rookie/johns-car-project/Assets/2014_8_4_gauge_320X240.bmp

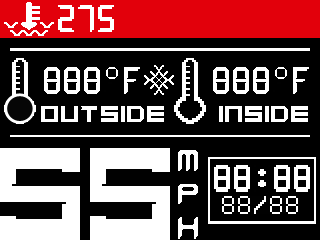
Assets/2014_8_4_gauge_320X240.bmp
