rookie/johns-car-project/Assets/gauge1.bmp

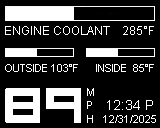
Assets/gauge1.bmp
