rookie/johns-car-project/Processing/JohnsCarProjectUI/gaugev1.bmp

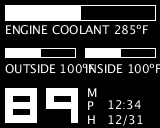
Processing/JohnsCarProjectUI/gaugev1.bmp
