rookie/johns-car-project/johnsCarProject/smallFont.ino

//16x12
const unsigned char PROGMEM icon_degree[] =
{
  B00011111, B10000000,
  B00111111, B11000000,
  B01100000, B01100000,
  B11000000, B00110000,
  B11000000, B00110000,
  B11000000, B00110000,
  B11000000, B00110000,
  B11000000, B00110000,
  B11000000, B00110000,
  B01100000, B01100000,
  B00111111, B11000000,
  B00011111, B10000000,
};

//16x27
const unsigned char PROGMEM icon_negative[] =
{
  B00000000, B00000000,
  B00000000, B00000000,
  B00000000, B00000000,
  B00000000, B00000000,
  B00000000, B00000000,
  B00000000, B00000000,
  B00000000, B00000000,
  B00000000, B00000000,
  B00000000, B00000000,
  B00000000, B00000000,
  B00000000, B00000000,
  B00000000, B00000000,
  B00011111, B11111110,
  B00111111, B11111100,
  B01111111, B11111000,
  B00000000, B00000000,
  B00000000, B00000000,
  B00000000, B00000000,
  B00000000, B00000000,
  B00000000, B00000000,
  B00000000, B00000000,
  B00000000, B00000000,
  B00000000, B00000000,
  B00000000, B00000000,
  B00000000, B00000000,
  B00000000, B00000000,
  B00000000, B00000000,
};


//16x27
const unsigned char PROGMEM icon_f[] =
{
  B11111111, B11111111,
  B11111111, B11111111,
  B11111111, B11111110,
  B11111111, B11111100,
  B11110000, B00000000,
  B11110000, B00000000,
  B11110000, B00000000,
  B11110000, B00000000,
  B11110000, B00000000,
  B11110000, B00000000,
  B11110000, B00000000,
  B11100000, B00000000,
  B11111111, B11110000,
  B11111111, B11100000,
  B11111111, B11000000,
  B11100000, B00000000,
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
{
  tft.drawBitmap(x, y,  icon_small7, 16, 27, fgColor, bgColor);
}

void tftdrawSmall8(int x, int y)
{
  tft.drawBitmap(x, y,  icon_small8, 16, 27, fgColor, bgColor);
}

void tftdrawSmall9(int x, int y)
{
  tft.drawBitmap(x, y,  icon_small9, 16, 27, fgColor, bgColor);
}

void tftdrawTextSmall(int x, int y, char c)
{
  switch (c) {
    case '0':
      tftdrawSmall0(x, y);
    break;
    case '1':
      tftdrawSmall1(x, y);
    break;
    case '2':
      tftdrawSmall2(x, y);
    break;
    case '3':
      tftdrawSmall3(x, y);
    break;
    case '4':
      tftdrawSmall4(x, y);
    break;
    case '5':
      tftdrawSmall5(x, y);
    break;
    case '6':
      tftdrawSmall6(x, y);
    break;
    case '7':
      tftdrawSmall7(x, y);
    break;
    case '8':
      tftdrawSmall8(x, y);
    break;
    case '9':
      tftdrawSmall9(x, y);
    break;
    case '-':
      tftdrawNegative(x, y);
    break;
    default:
      tftdrawSmallBlank(x, y);
    break;
  }
}
