rookie/johns-car-project/johnsCarProject/symbols.ino

//96x16
const unsigned char PROGMEM icon_inside[] =
{ B11110011, B11111111, B11111000, B00001111, B11111111, B11100011, B11001111, B11111111, B11000000, B00111111, B11111111, B10000000,
  B11110011, B11111111, B11111100, B00011111, B11111111, B11100011, B11001111, B11111111, B11100000, B01111111, B11111111, B10000000,
  B11110011, B11111111, B11111110, B00111111, B11111111, B11100011, B11001111, B11111111, B11110000, B11111111, B11111111, B10000000,
  B11110011, B11000000, B00011110, B00111111, B11111111, B11100011, B11001111, B00000000, B01111000, B11111111, B11111111, B10000000,
  B11110011, B11000000, B00011110, B00111100, B00000000, B00000011, B11001111, B00000000, B01111000, B11110000, B00000000, B00000000,
  B11110011, B11000000, B00011110, B00111100, B00000000, B00000011, B11001111, B00000000, B01111000, B11110000, B00000000, B00000000,
  B11110011, B11000000, B00011110, B00111111, B11111111, B10000011, B11001111, B00000000, B01111000, B11111111, B11111110, B00000000,
  B11110011, B11000000, B00011110, B00111111, B11111111, B11000011, B11001111, B00000000, B01111000, B11111111, B11111111, B00000000,
  B11110011, B11000000, B00011110, B00011111, B11111111, B11100011, B11001111, B00000000, B01111000, B11111111, B11111111, B00000000,
  B11110011, B11000000, B00011110, B00001111, B11111111, B11100011, B11001111, B00000000, B01111000, B11111111, B11111110, B00000000,
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
void tftdrawTherm(int x, int y)
{
  tft.drawBitmap(x, y,  icon_therm, 32, 70, fgColor);
}

void tftdrawSnowflake(int x, int y)
{
  tft.drawBitmap(x, y,  icon_snowflake, 32, 30, fgColor);
}

void tftdrawCoolant(int x, int y, uint16_t color)
{
  tft.drawBitmap(x, y,  icon_coolant, 40, 39, color);
}
