rookie/johns-car-project/Processing/gridDrawToArray/binary.pde

private static final int B0 = 0;
private static final int B00 = 0;
private static final int B000 = 0;
private static final int B0000 = 0;
private static final int B00000 = 0;
private static final int B000000 = 0;
private static final int B0000000 = 0;
private static final int B00000000 = 0;
private static final int B1 = 1;
private static final int B01 = 1;
private static final int B001 = 1;
private static final int B0001 = 1;
private static final int B00001 = 1;
private static final int B000001 = 1;
private static final int B0000001 = 1;
private static final int B00000001 = 1;
private static final int B10 = 2;
private static final int B010 = 2;
private static final int B0010 = 2;
private static final int B00010 = 2;
private static final int B000010 = 2;
private static final int B0000010 = 2;
private static final int B00000010 = 2;
private static final int B11 = 3;
private static final int B011 = 3;
private static final int B0011 = 3;
private static final int B00011 = 3;
private static final int B000011 = 3;
private static final int B0000011 = 3;
private static final int B00000011 = 3;
private static final int B100 = 4;
private static final int B0100 = 4;
private static final int B00100 = 4;
private static final int B000100 = 4;
private static final int B0000100 = 4;
private static final int B00000100 = 4;
private static final int B101 = 5;
private static final int B0101 = 5;
private static final int B00101 = 5;
private static final int B000101 = 5;
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
private static final int B11111001 = 249;
private static final int B11111010 = 250;
private static final int B11111011 = 251;
private static final int B11111100 = 252;
private static final int B11111101 = 253;
private static final int B11111110 = 254;
private static final int B11111111 = 255;
